thisoldgeek/miniz/textures/clock_face.png

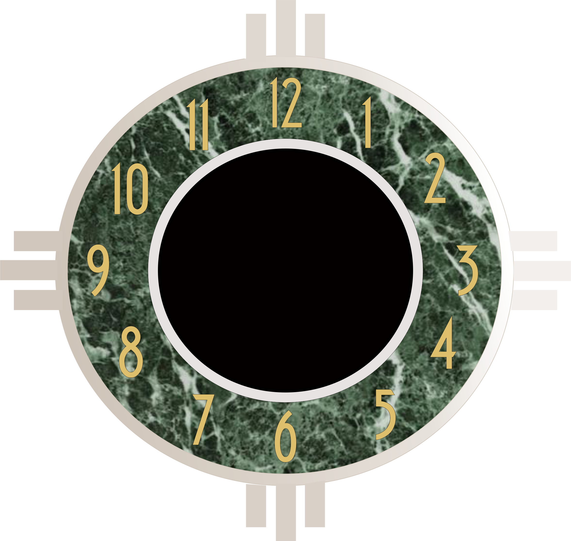
textures/clock_face.png
