thisoldgeek/miniz/textures/default_cover.png

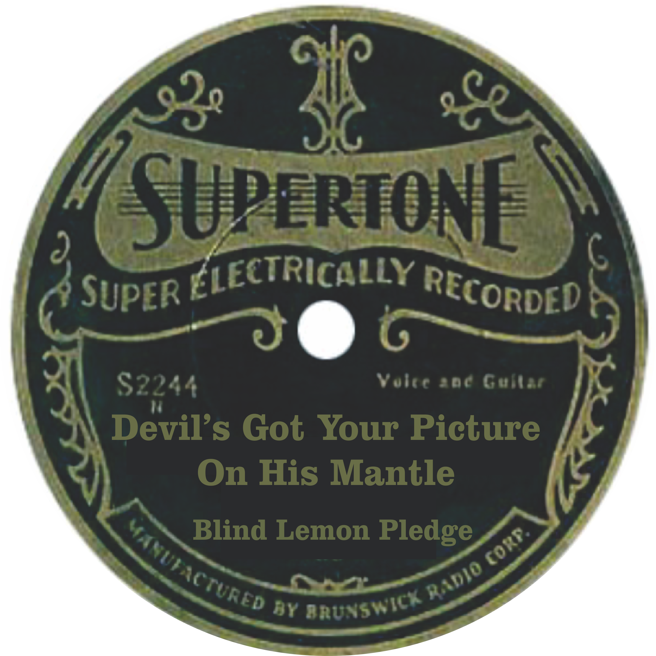
textures/default_cover.png
