thisoldgeek/miniz/textures/dial.png

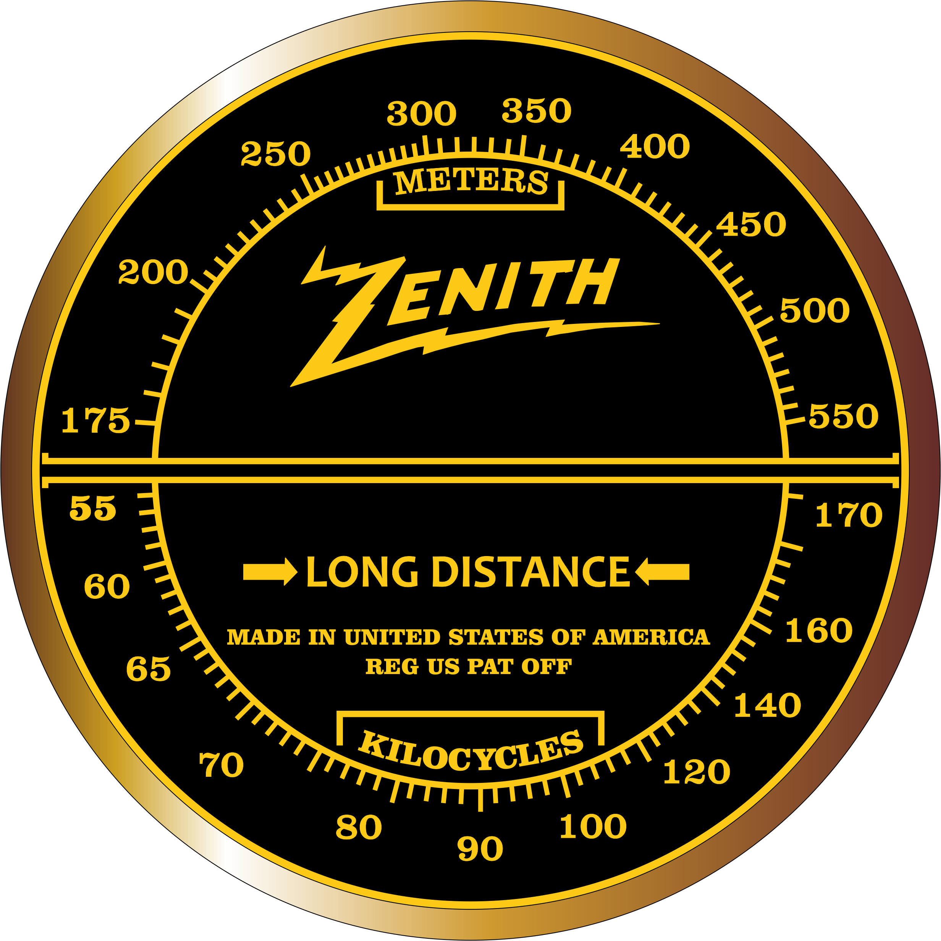
textures/dial.png
