thisoldgeek/miniz/textures/needle.png

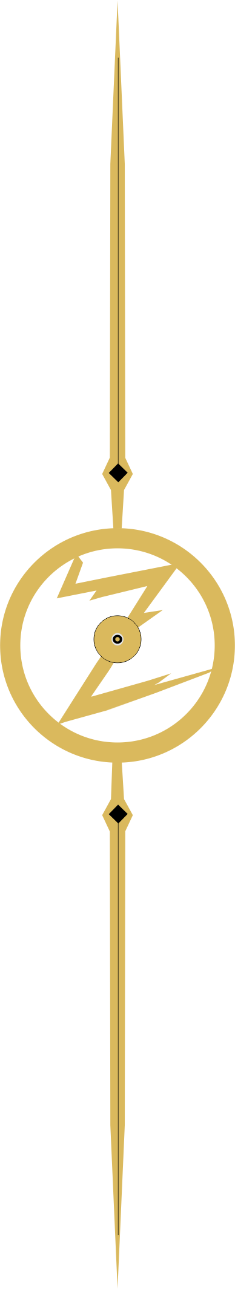
textures/needle.png
