thisoldgeek/miniz/docs/miniz_wiring_bonnet.png

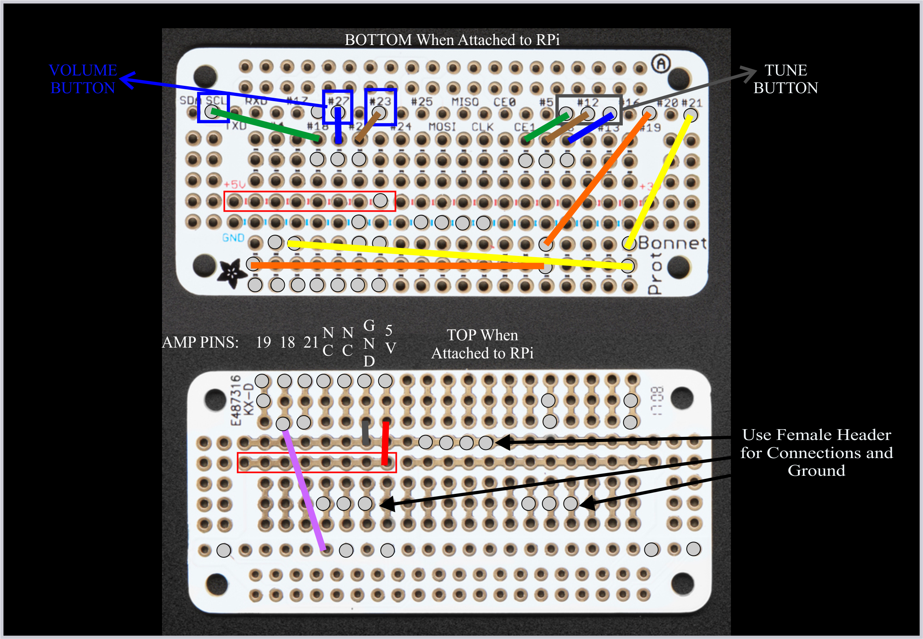
docs/miniz_wiring_bonnet.png
